pyzahl/SSSM4CircuitPython/PXL_20230120_041340795.jpg

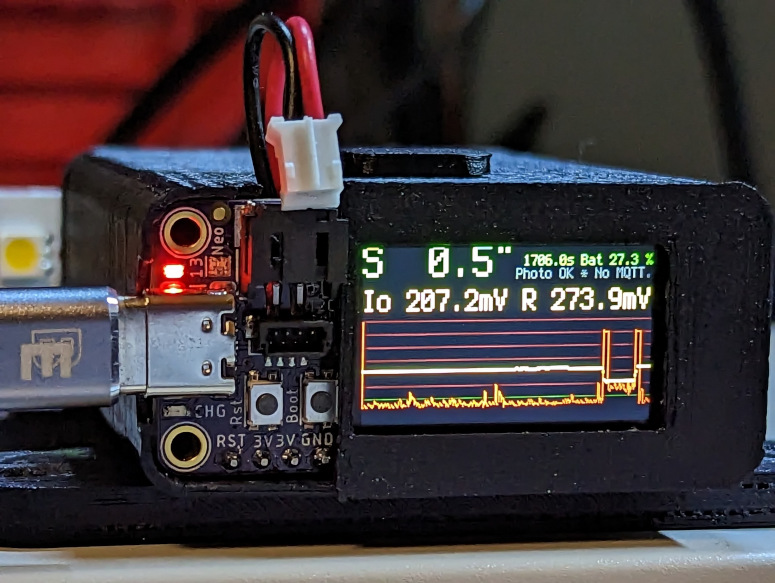
PXL_20230120_041340795.jpg
