pyzahl/SSSM4CircuitPython/WhatsApp Image 2023-01-28 at 11.27.37.jpeg

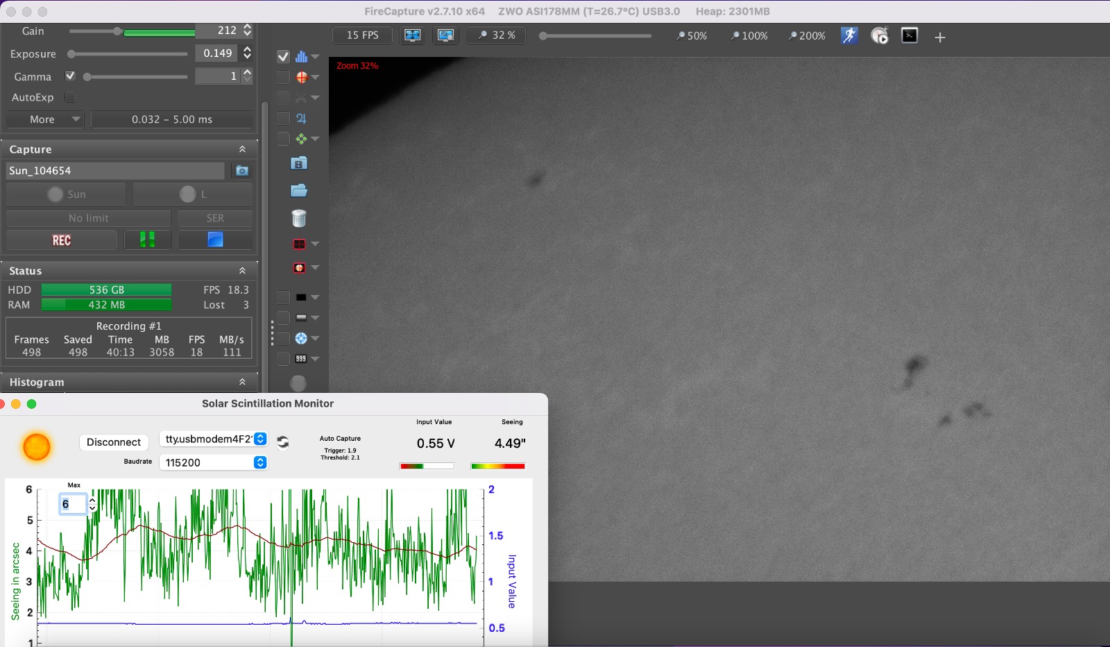
WhatsApp Image 2023-01-28 at 11.27.37.jpeg
