pyzahl/SSSM4CircuitPython/case_3d_print/SSSM-Feather-ESP32-S3-TFT-box-Ap00-dual.stl

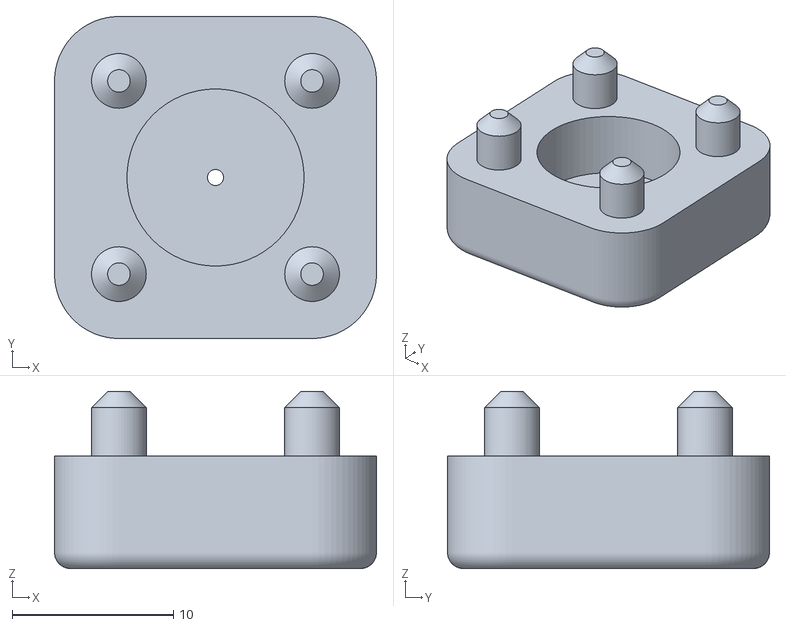
[picture p21: CAD file, 2023-01-28]
case_3d_print/SSSM-Feather-ESP32-S3-TFT-box-Ap00-dual.stl
20.0 x 20.0 x 11.0
