pyzahl/SSSM4CircuitPython/case_3d_print/SSSM-Feather-ESP32-S3-TFT-box.stp

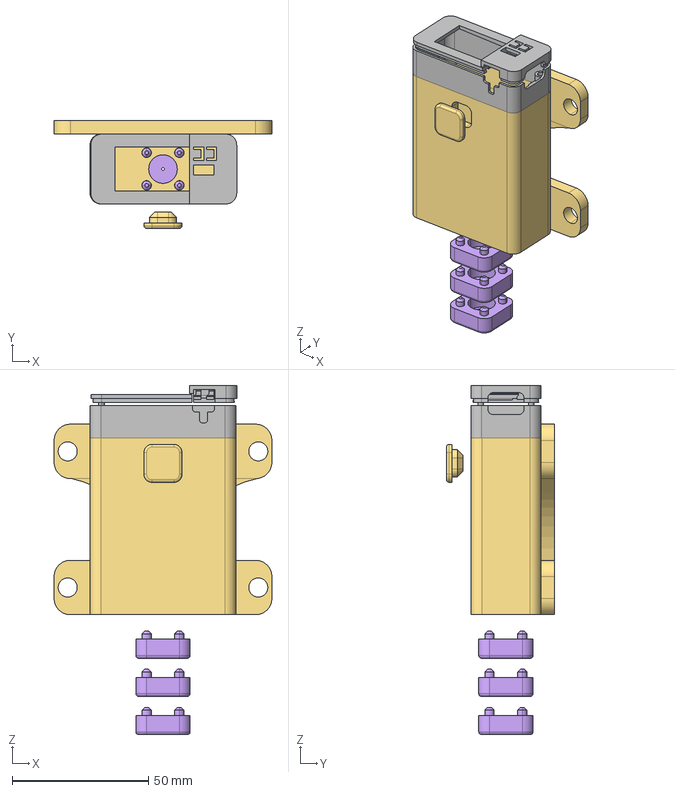
[picture p22: CAD file, 2023-01-15]
case_3d_print/SSSM-Feather-ESP32-S3-TFT-box.stp
80.0 x 39.7 x 128.2 mm
Feather TFT v93
Feather TFT v92
