pyzahl/SSSM4CircuitPython/case_3d_print/SSSM-Feather-ESP32-S3-TFT-box-w-hole.stl

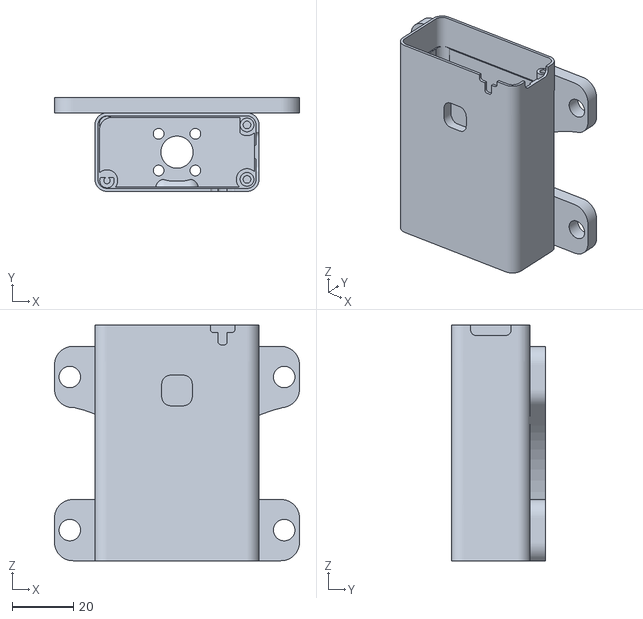
[picture p23: CAD file, 2023-01-15]
case_3d_print/SSSM-Feather-ESP32-S3-TFT-box-w-hole.stl
80.0 x 30.7 x 76.9
