pyzahl/SSSM4CircuitPython/case_3d_print/SSSM-Feather-ESP32-S3-TFT-box-Ap3mm.stl

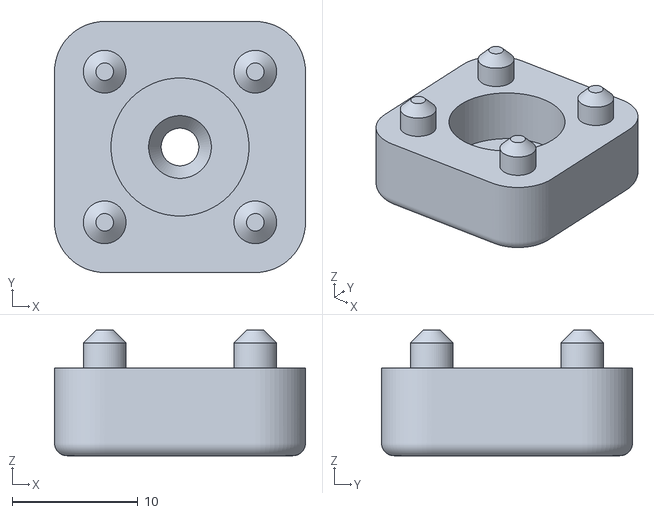
[picture p24: CAD file, 2023-01-15]
case_3d_print/SSSM-Feather-ESP32-S3-TFT-box-Ap3mm.stl
20.0 x 20.0 x 10.0
