pyzahl/SSSM4CircuitPython/case_3d_print/SSSM-Feather-ESP32-S3-TFT-box-A.stp

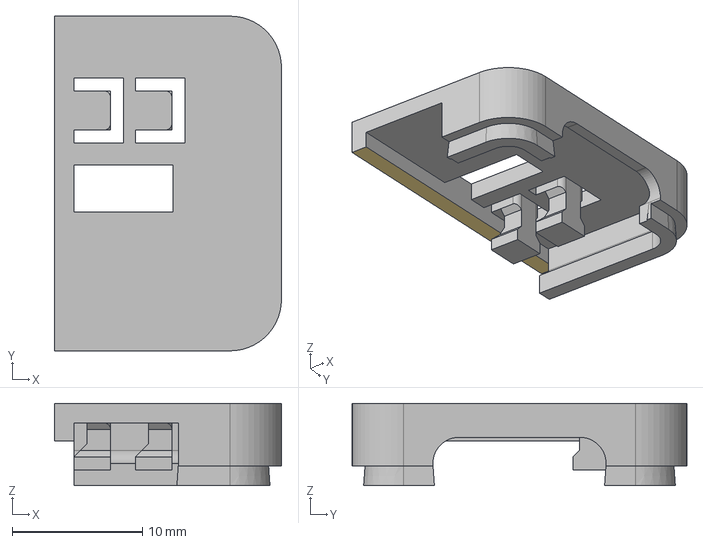
[picture p25: CAD file, 2023-01-15]
case_3d_print/SSSM-Feather-ESP32-S3-TFT-box-A.stp
17.4 x 25.7 x 6.30 mm
