pyzahl/SSSM4CircuitPython/case_3d_print/SSSM-Feather-ESP32-S3-TFT-box-B.stp

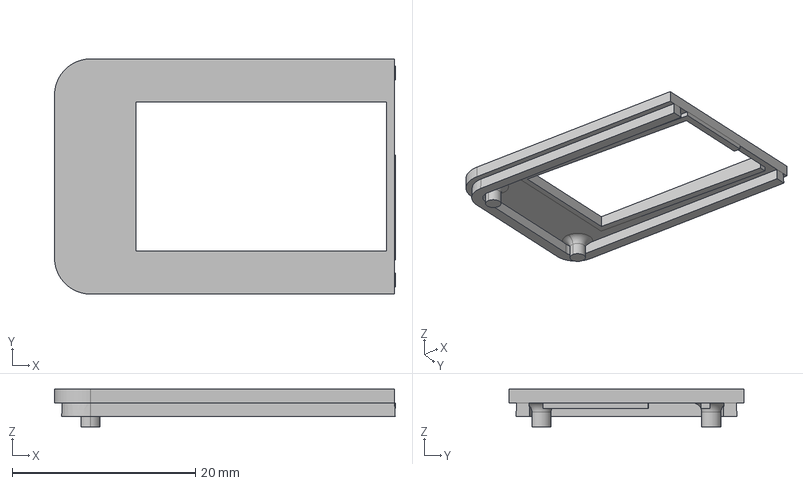
[picture p26: CAD file, 2023-01-15]
case_3d_print/SSSM-Feather-ESP32-S3-TFT-box-B.stp
37.2 x 25.7 x 4.10 mm
