pyzahl/SSSM4CircuitPython/case_3d_print/Feather TFT.step

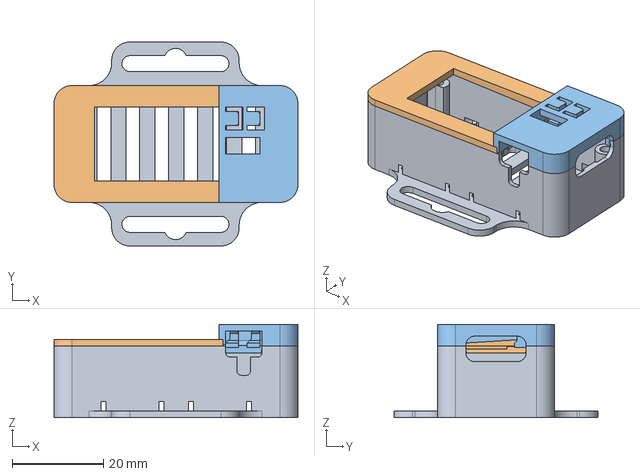
[picture p27: CAD file, 2023-01-15]
case_3d_print/Feather TFT.step
53.6 x 44.8 x 20.5 mm
