pyzahl/SSSM4CircuitPython/case_3d_print/SSSM-Feather-ESP32-S3-TFT-box-SW-Lid.stl

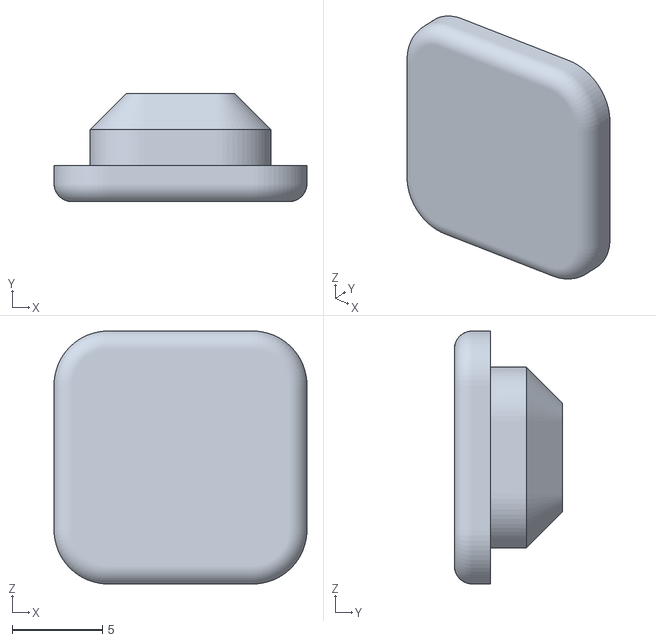
[picture p28: CAD file, 2023-01-15]
case_3d_print/SSSM-Feather-ESP32-S3-TFT-box-SW-Lid.stl
14.0 x 6.00 x 14.0
