pyzahl/SSSM4CircuitPython/CP-drive/secrets.py

# This file is where you keep secret settings, passwords, and tokens!
# If you put them in the code you risk committing that info or sharing it

secrets = {
    'ssid' : 'YOURNETWORKSSID',
    'password' : 'YOURWIFIPASSWORD',
    'timezone' : "America/New_York", # http://worldtimeapi.org/timezones
    'broker' : 'io.adafruit.com', # or your own local broker's IP
    'port' : 1883,
    'aio_username' : 'username',
    'aio_key' : 'aio_userkeykeykeyxxxxxxx',
    }
    
